SimonBrenninger/smartWatch/pcb/docs/20230504_111602.jpg

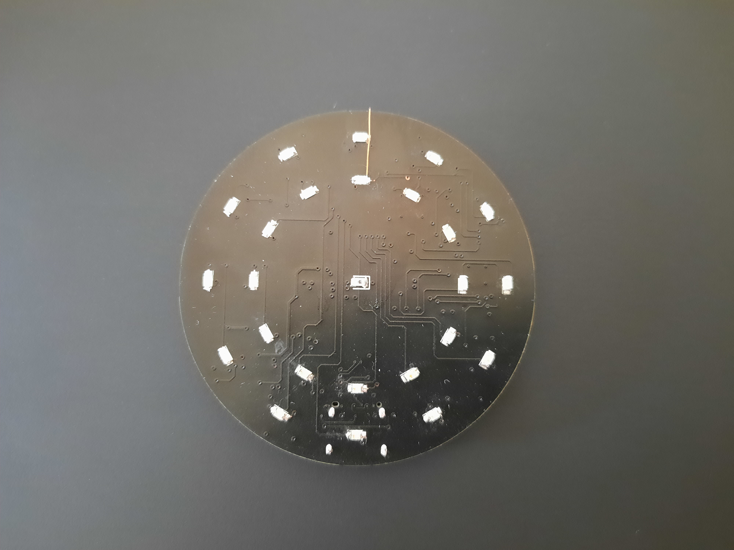
pcb/docs/20230504_111602.jpg
