SimonBrenninger/smartWatch/pcb/docs/pcb_v1.pdf

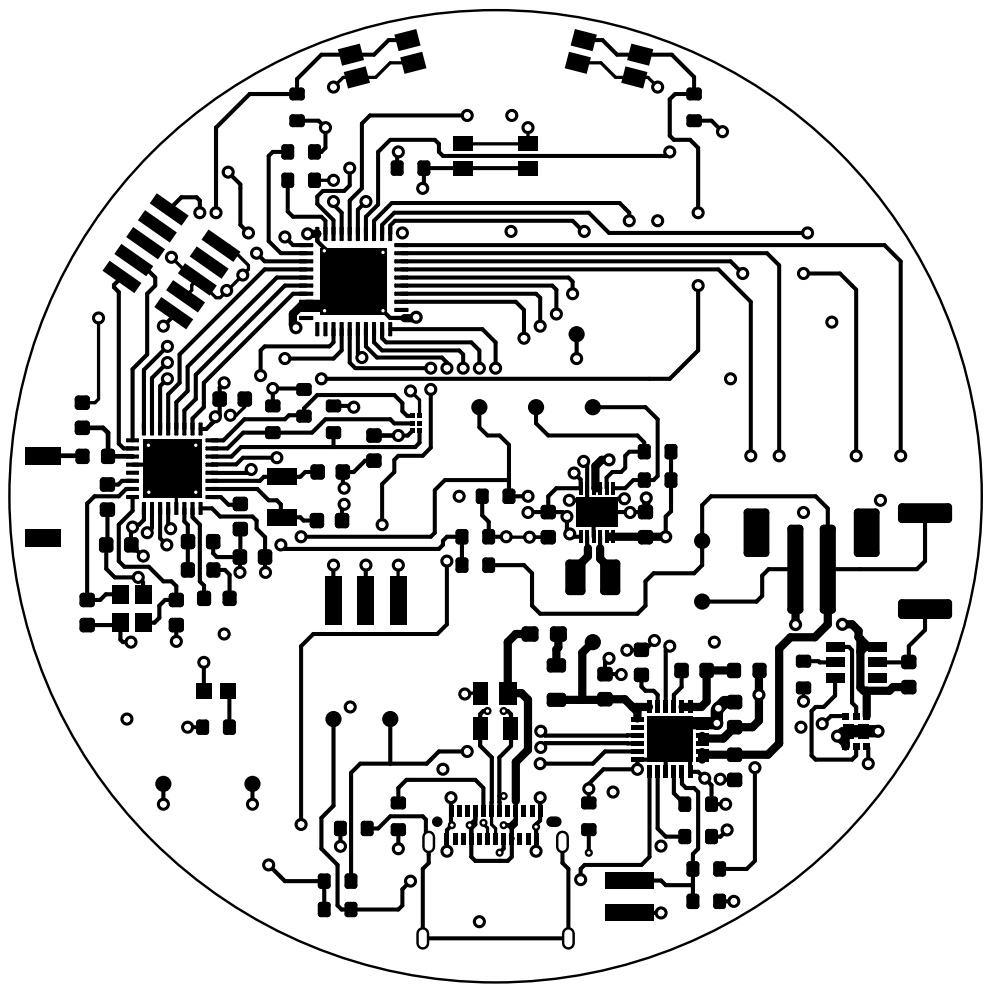
[picture p9: page 1]

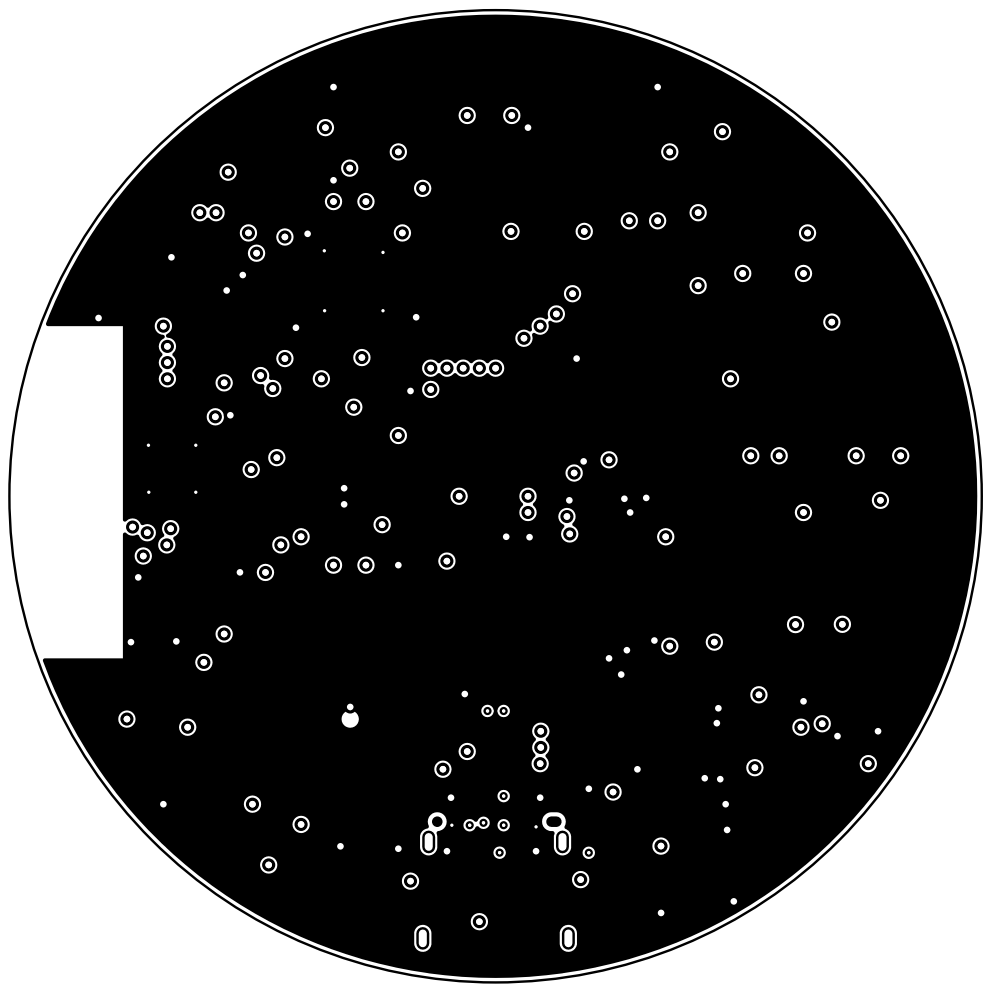
[picture p10: page 2]

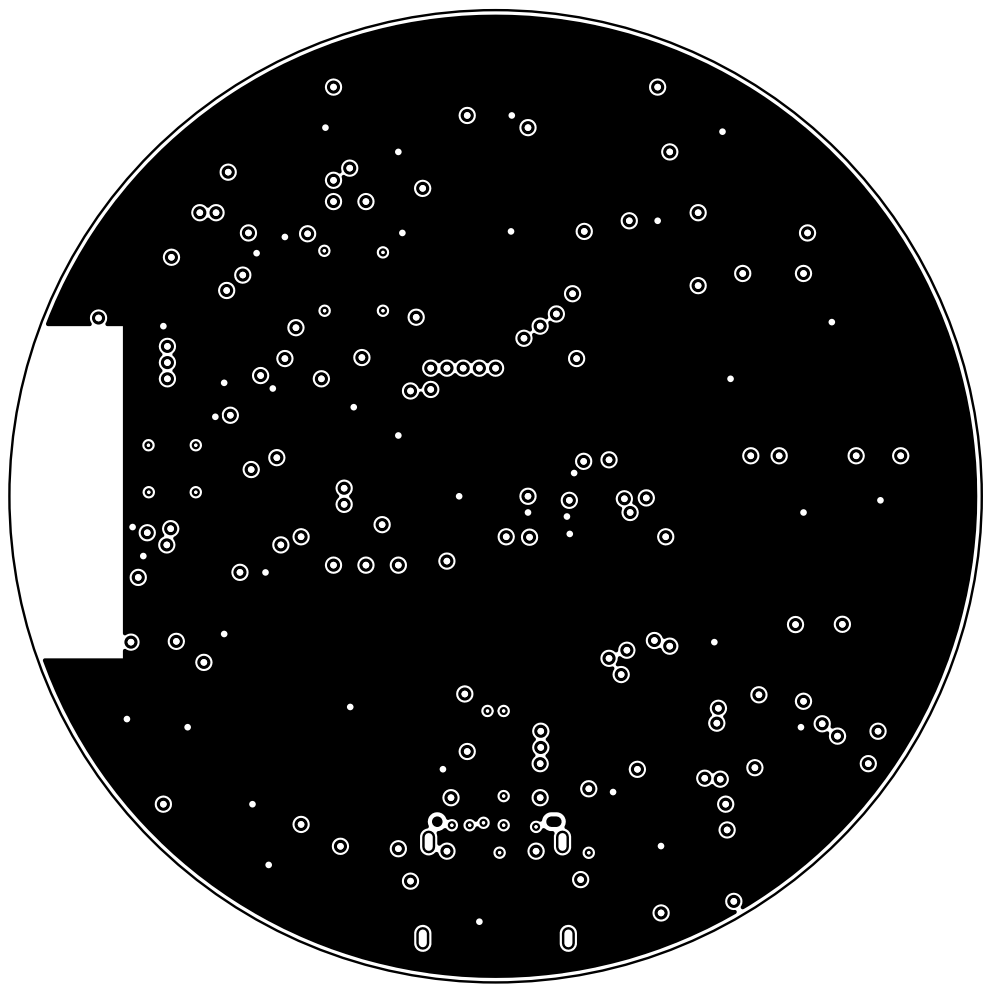
[picture p11: page 3]

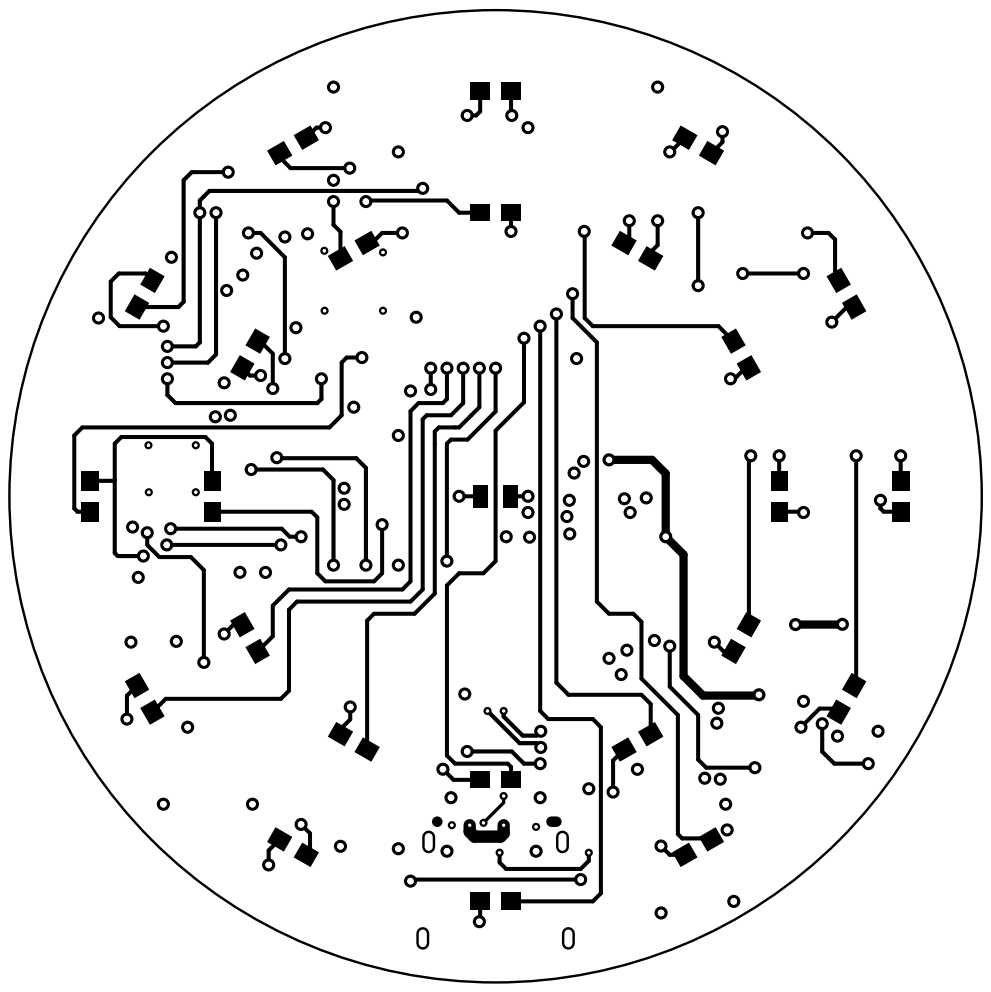
[picture p12: page 4]

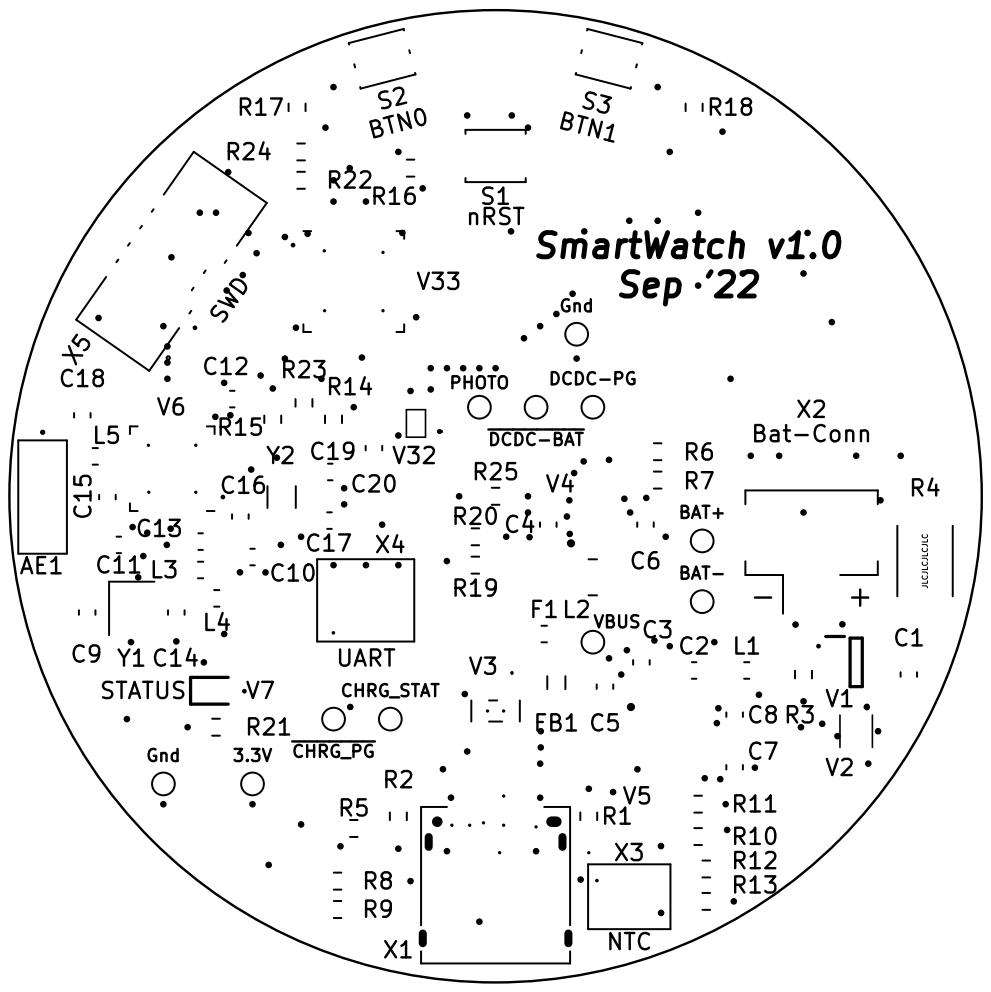
[picture p13: page 5]

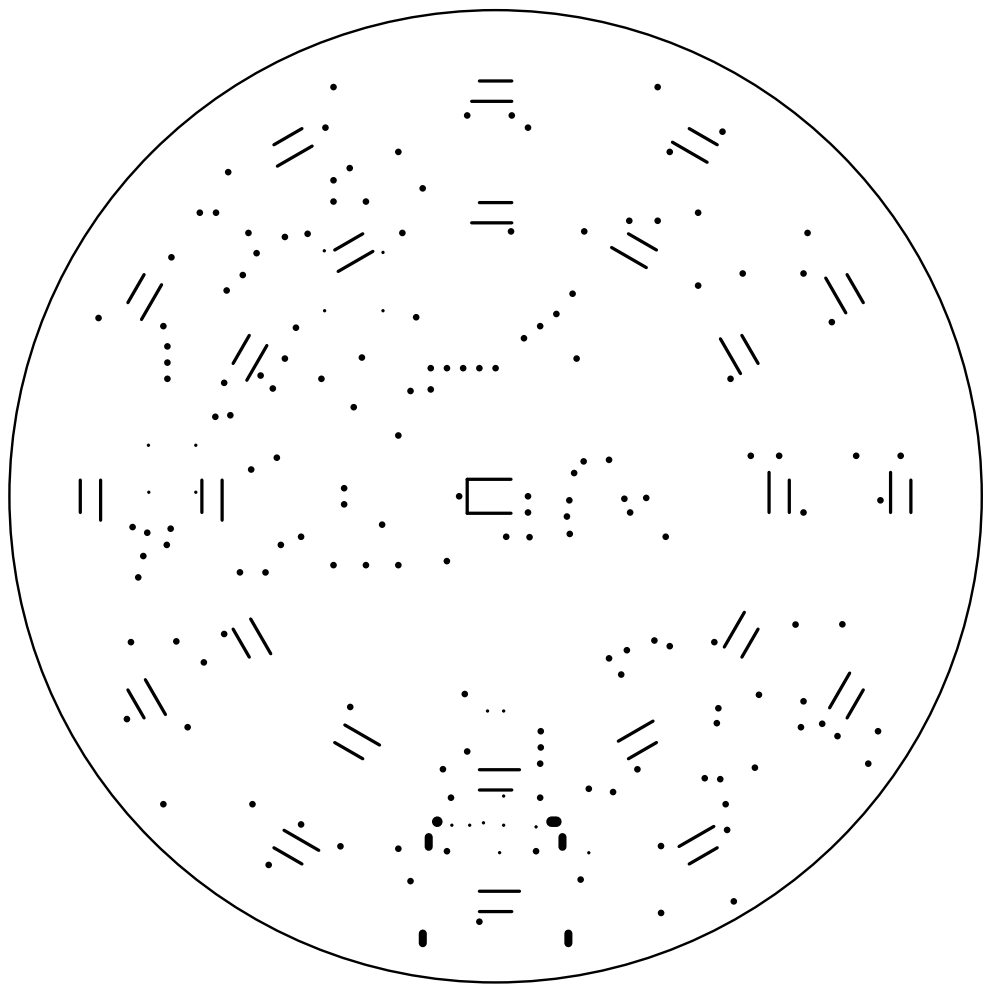
[picture p14: page 6]
